jswiles/MPPTSolarPwrModule_R2/Photos/IMG_0883.JPG

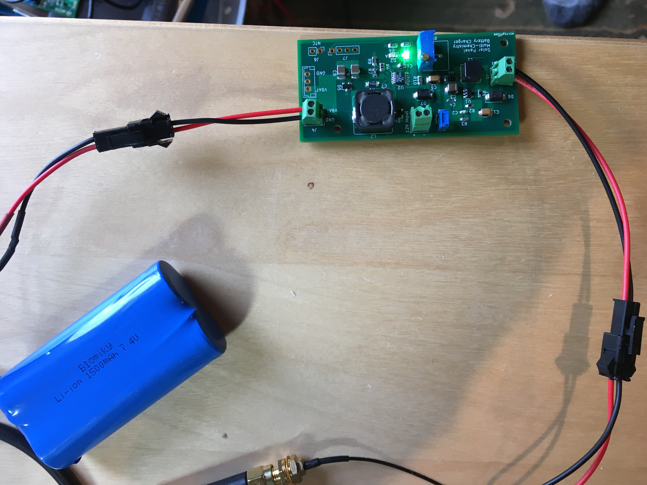
Photos/IMG_0883.JPG
